bobis1/learnboard/1000_F_471882407_iQw7ESR0eo3HU8ldL6hmX6TLpr7Ehfek.jpg

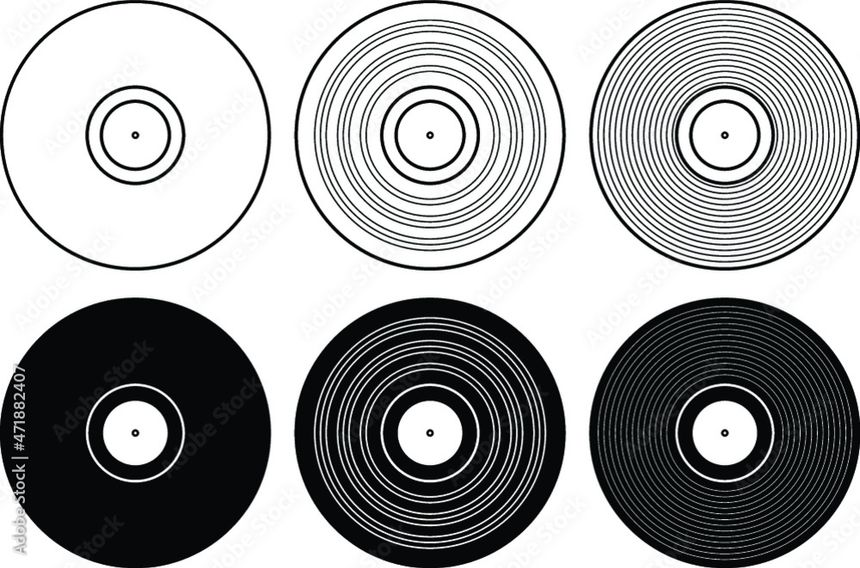
1000_F_471882407_iQw7ESR0eo3HU8ldL6hmX6TLpr7Ehfek.jpg
