bobis1/learnboard/musical-note-clef-staff-bass-music-notes-png-thumbnail-removebg-preview.png

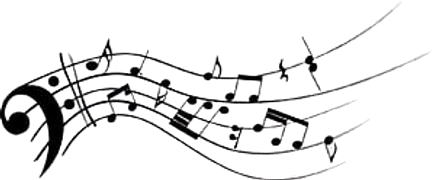
musical-note-clef-staff-bass-music-notes-png-thumbnail-removebg-preview.png
