bobis1/learnboard/poster/DraftRenders/Final.png

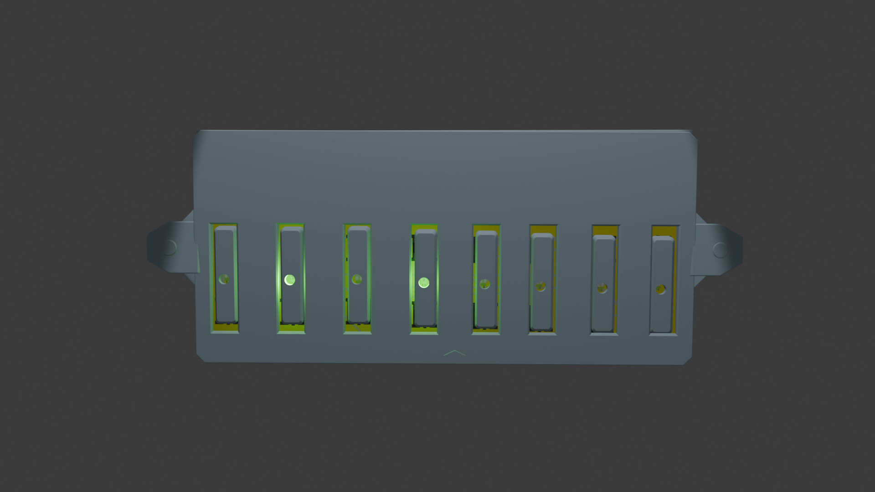
poster/DraftRenders/Final.png
