bobis1/learnboard/poster/DraftRenders/FinalRenderpng.png

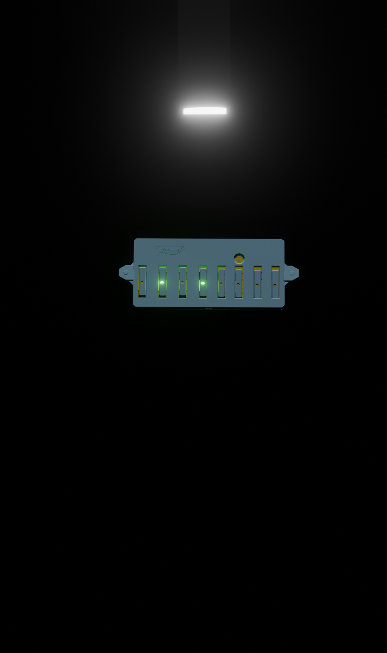
poster/DraftRenders/FinalRenderpng.png
