bobis1/learnboard/poster/DraftRenders/First.png

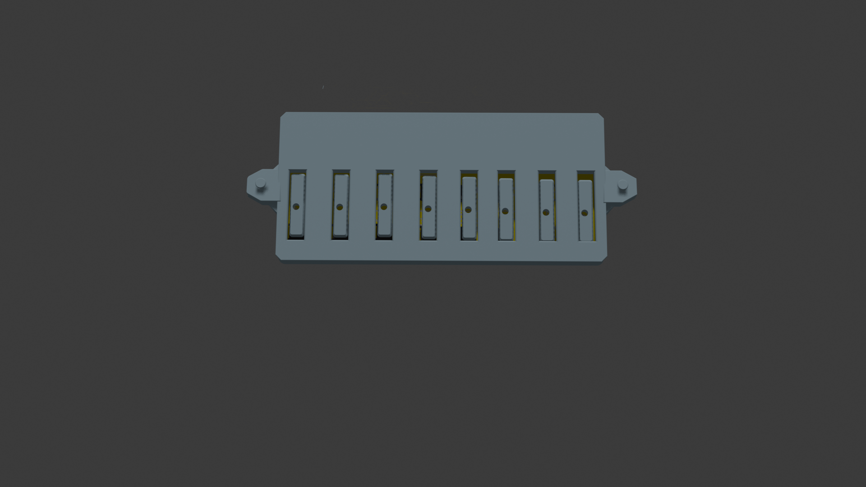
poster/DraftRenders/First.png
