bobis1/learnboard/poster/DraftRenders/Render.png

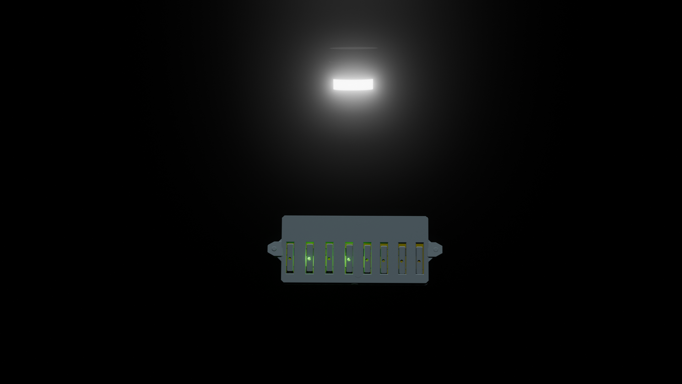
poster/DraftRenders/Render.png
