bobis1/learnboard/poster/DraftRenders/SpotlightWithLearnboardRender.png

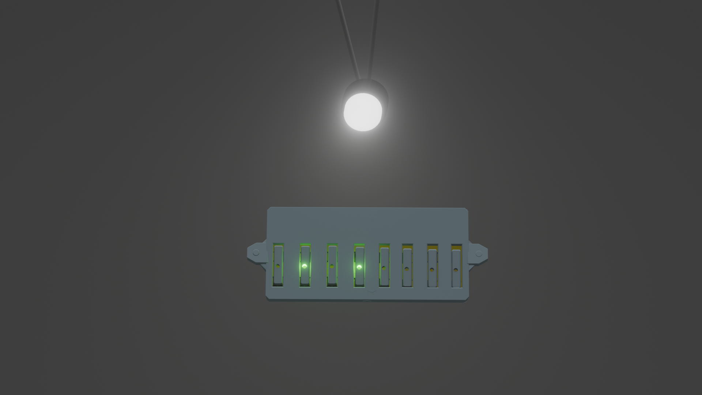
poster/DraftRenders/SpotlightWithLearnboardRender.png
