bobis1/learnboard/poster/Posterassets/LightRenderTransparentWLight.png

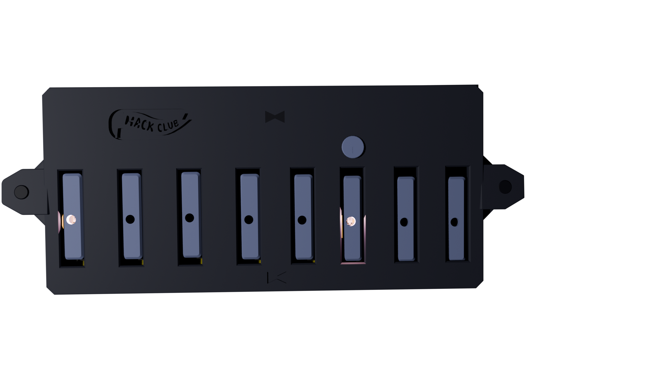
poster/Posterassets/LightRenderTransparentWLight.png
