bobis1/learnboard/poster/Posterassets/spotlight.png

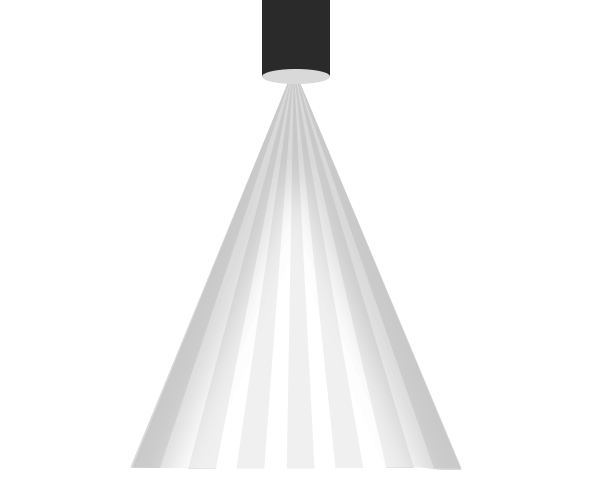
poster/Posterassets/spotlight.png
