bobis1/learnboard/ReadmeAssets/3D-model.png

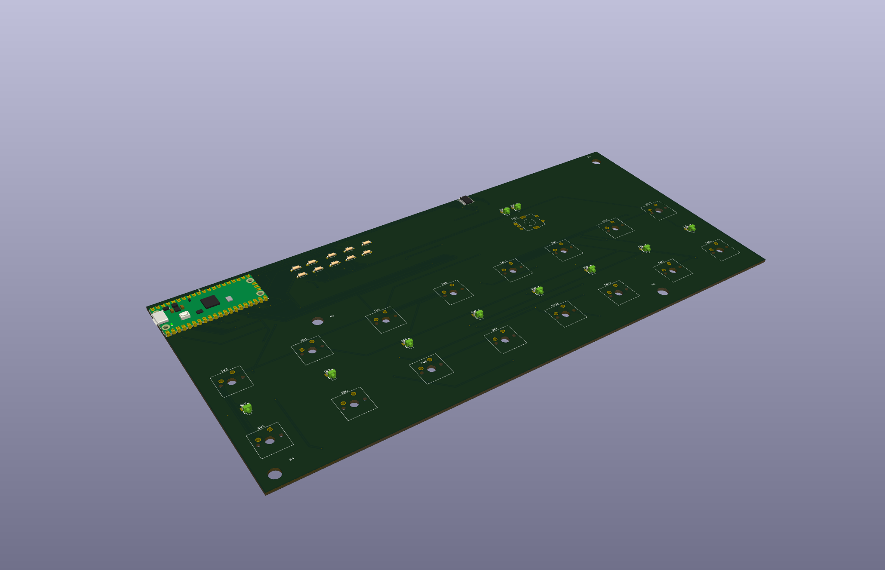
ReadmeAssets/3D-model.png
