bobis1/learnboard/ReadmeAssets/PCBrend.png

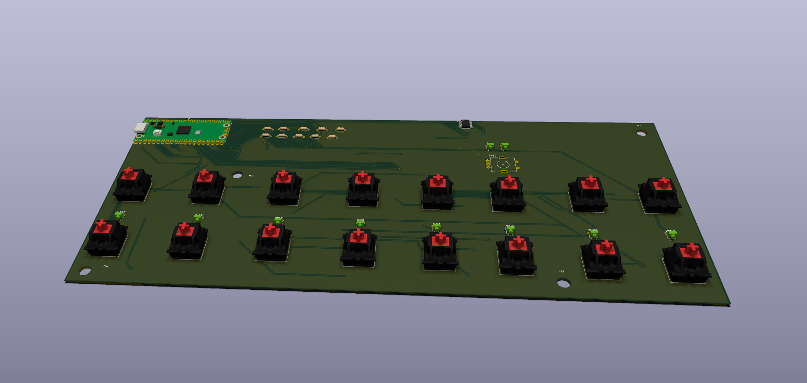
ReadmeAssets/PCBrend.png
