bobis1/learnboard/JournalPictures/32862.jpg

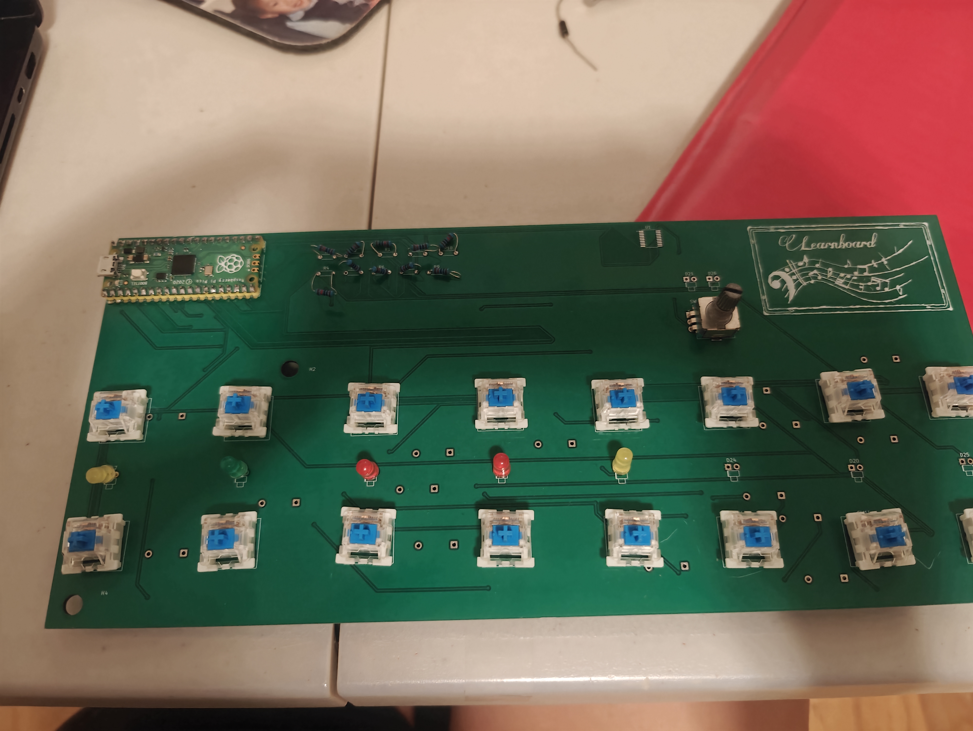
JournalPictures/32862.jpg
