bobis1/learnboard/JournalPictures/Screenshot 2026-09-02 at 8.49.35 PM.png

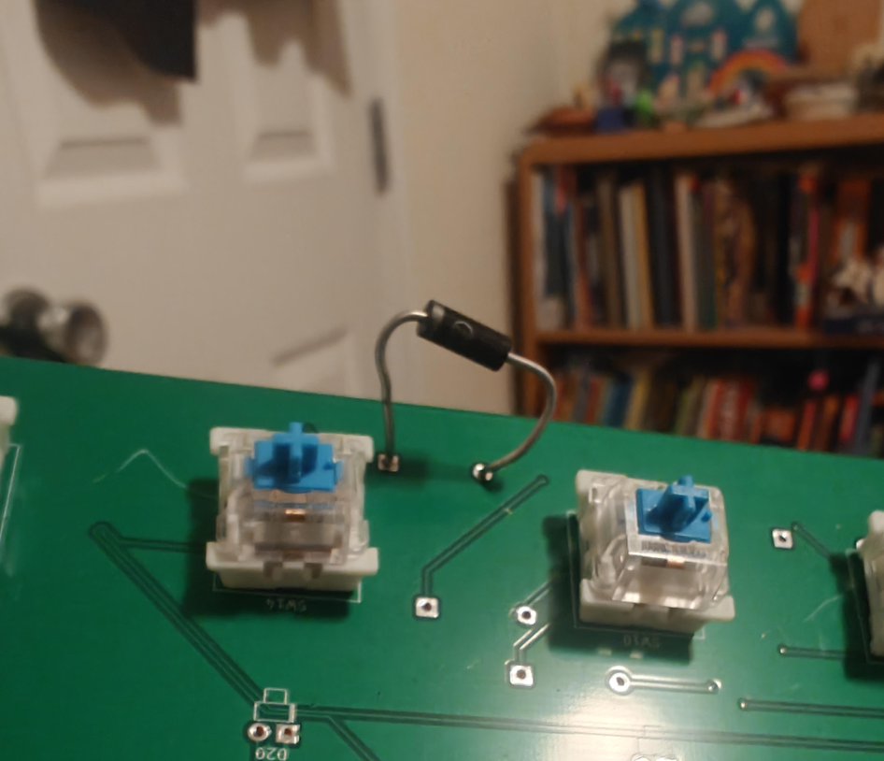
JournalPictures/Screenshot 2026-09-02 at 8.49.35 PM.png
